twinking92/Olympische-Ringe/images/IMG_20191116_184240.jpg

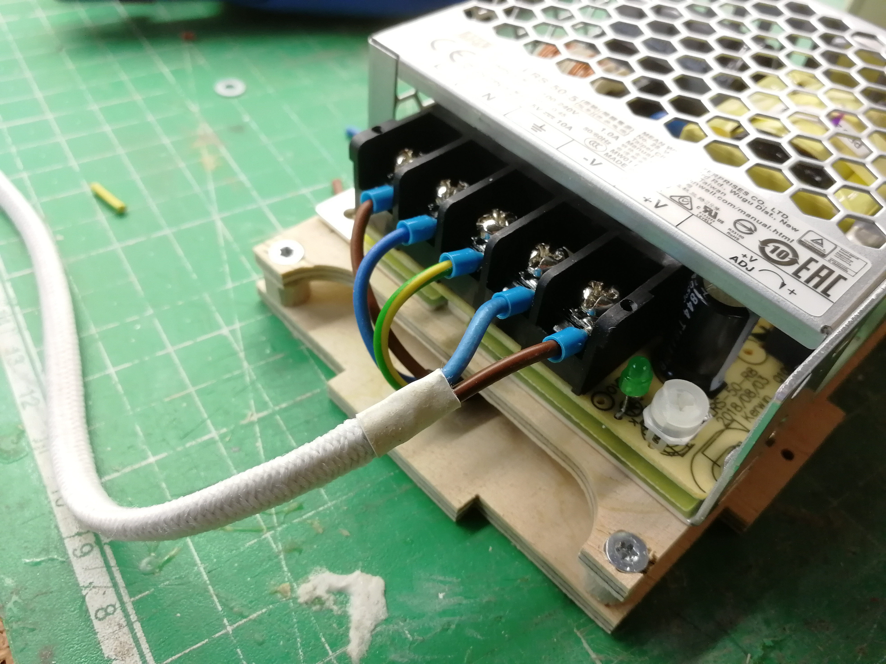
images/IMG_20191116_184240.jpg
